carbon-speed/DRK-1/3-D_Printing_Files/11.Camera_Pin.STL

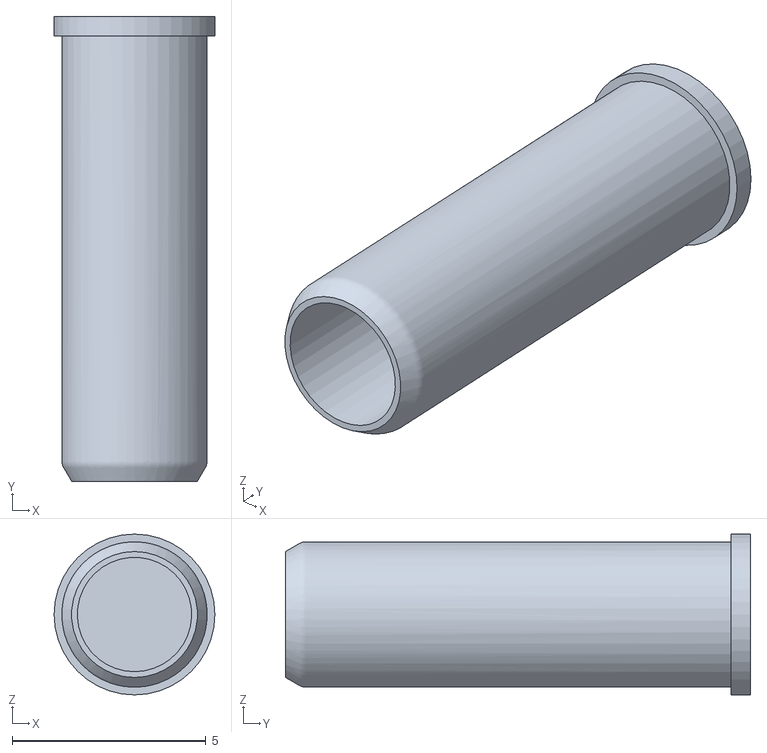
[picture p59: CAD file, 2022-08-29]
3-D_Printing_Files/11.Camera_Pin.STL
4.15 x 12.0 x 4.15
