carbon-speed/DRK-1/SolidworksCAD/5.Camera_Mount.SLDPRT

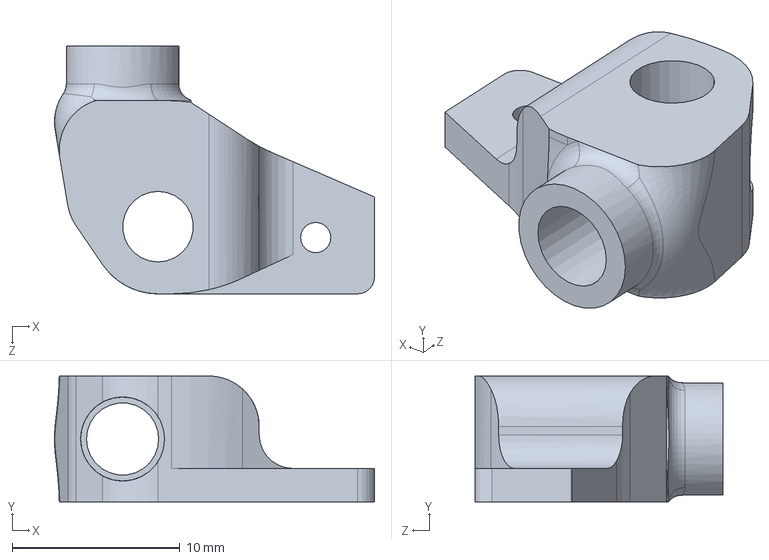
[picture p60: CAD file, 2022-08-29]
SolidworksCAD/5.Camera_Mount.SLDPRT
19.1 x 7.50 x 14.8 mm
